s51517765/Tibicon/img/1.jpg

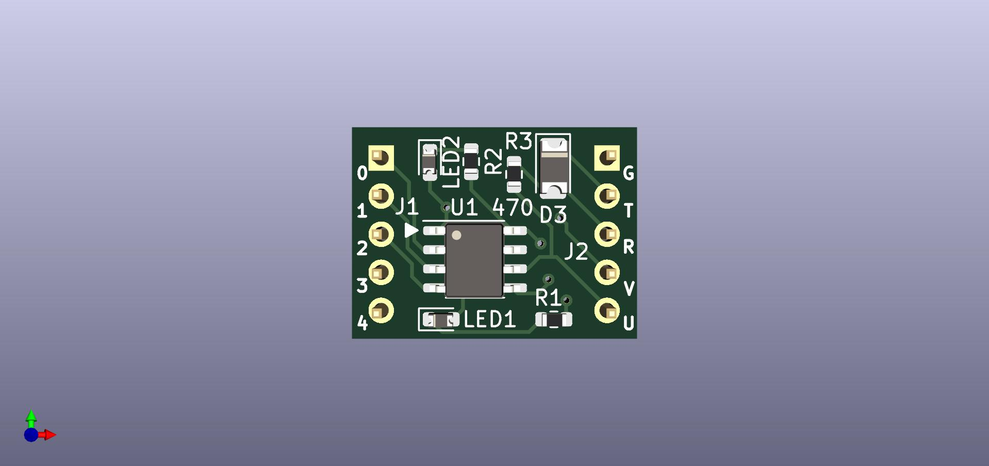
img/1.jpg
